aidanmacro/MYOSA-Breath-Activity-Monitoring-for-Musicians/Code/MYOSA_code/I2C_ADC_WiFi/splash.h

#define splash1_width 82
#define splash1_height 64

const uint8_t PROGMEM splash1_data[] = {
    B00000000, B00000000, B00000000, B00000000, B00000000, B00000001, B10000000,
    B00000000, B00000000, B00000000, B00000000, B00000000, B00000000, B00000000,
    B00000000, B00000000, B00000011, B10000000, B00000000, B00000000, B00000000,
    B00000000, B00000000, B00000000, B00000000, B00000000, B00000000, B00000111,
    B11000000, B00000000, B00000000, B00000000, B00000000, B00000000, B00000000,
    B00000000, B00000000, B00000000, B00000111, B11000000, B00000000, B00000000,
    B00000000, B00000000, B00000000, B00000000, B00000000, B00000000, B00000000,
    B00001111, B11000000, B00000000, B00000000, B00000000, B00000000, B00000000,
    B00000000, B00000000, B00000000, B00000000, B00011111, B11100000, B00000000,
    B00000000, B00000000, B00000000, B00000000, B00000000, B00000000, B00000000,
    B00000000, B00011111, B11100000, B00000000, B00000000, B00000000, B00000000,
    B00000000, B00000000, B00000000, B00000000, B00000000, B00111111, B11100000,
    B00000000, B00000000, B00000000, B00000000, B00000000, B00000000, B00000000,
    B00000000, B00000000, B00111111, B11110000, B00000000, B00000000, B00000000,
    B00000000, B00000000, B00000000, B00000000, B00000000, B00000000, B01111111,
    B11110000, B00000000, B00000000, B00000000, B00000000, B00000000, B00000000,
    B00000000, B00011111, B11111000, B01111111, B11110000, B00000000, B00000000,
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
    B11111110, B11110011, B10111100, B00111101, B11101111, B11100000, B00011111,
    B11111110, B01111111, B11111111, B01111111, B11111011, B11111111, B11011111,
    B11111110, B11111110, B11111111, B10111100, B00111101, B11101111, B11100000,
    B00011111, B11000110, B11111111, B11111111, B01111111, B11111011, B11111111,
    B11011111, B11111110, B11111110, B11111111, B10111100, B00111101, B11101111,
    B11100000, B00001111, B11100011, B11000111, B11111110, B01111000, B01111011,
    B11000011, B11011110, B00011110, B11110000, B11111111, B10111100, B00111101,
    B11101111, B00000000, B00000111, B11111111, B10000111, B11111100, B01111000,
    B01111011, B11000011, B11011110, B00011110, B11110000, B11111000, B00111100,
    B00111101, B11101111, B00000000, B00000001, B11111111, B11111111, B11110000,
    B00000000, B01111011, B11000011, B11000000, B00011110, B11110000, B11110000,
    B00111100, B00111101, B11101111, B00000000, B00000001, B11110011, B01111111,
    B11100000, B00111111, B11111011, B11000011, B11001111, B11111110, B11110000,
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
};
